andia89/MaraXEvolution-HMI/HMI/pictures/boiler_0.png

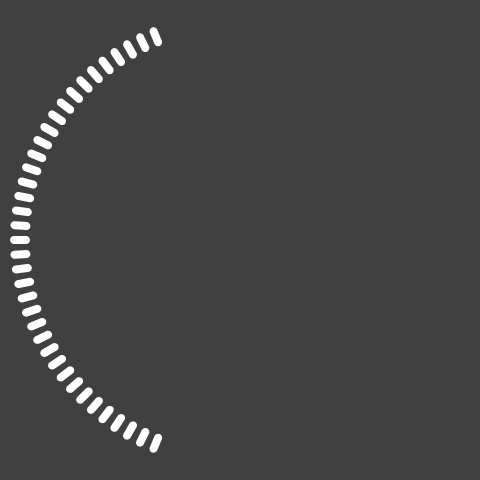
HMI/pictures/boiler_0.png
