andia89/MaraXEvolution-HMI/HMI/pictures/boiler_15.png

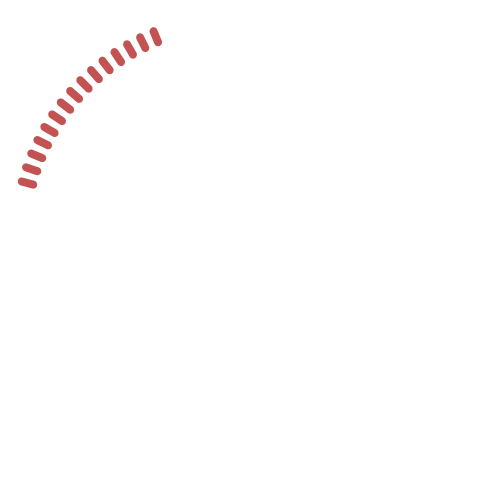
HMI/pictures/boiler_15.png
