andia89/MaraXEvolution-HMI/HMI/pictures/brew_0.png

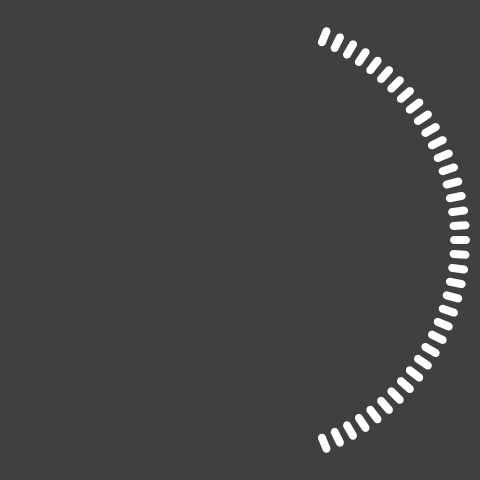
HMI/pictures/brew_0.png
