andia89/MaraXEvolution-HMI/HMI/pictures/brew_4.png

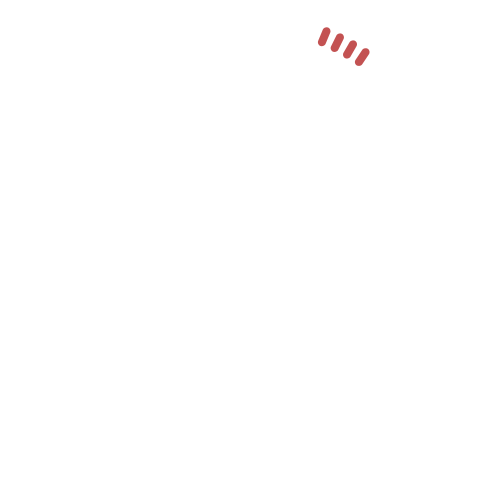
HMI/pictures/brew_4.png
