andia89/MaraXEvolution-HMI/HMI/pictures/brew_10.png

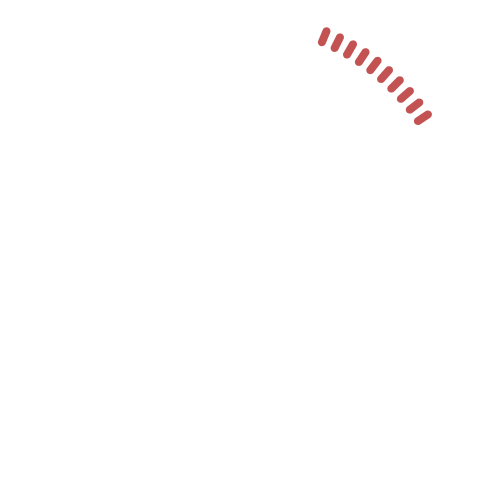
HMI/pictures/brew_10.png
