andia89/MaraXEvolution-HMI/HMI/pictures/brew_34.png

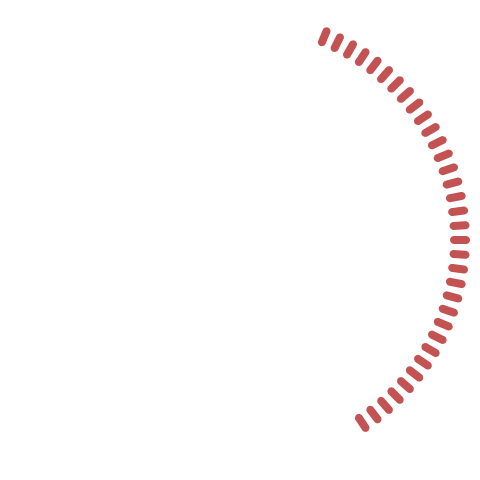
HMI/pictures/brew_34.png
