andia89/MaraXEvolution-HMI/HMI/pictures/chart.png

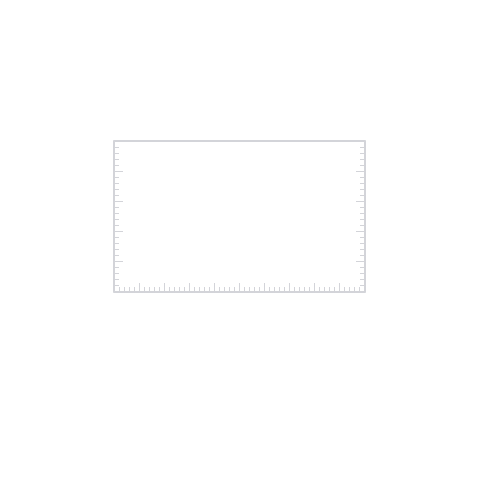
HMI/pictures/chart.png
