andia89/MaraXEvolution-HMI/HMI/pictures/circle.png

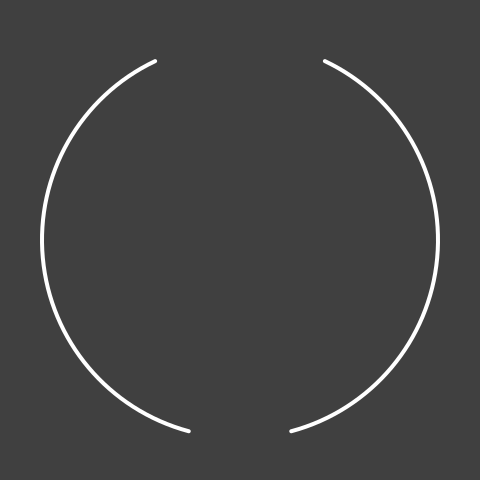
HMI/pictures/circle.png
